prydin/classab-amp/spice/class_ab.asc

C1: cap; 4.7n
C2: cap; 220p
C3: cap; 100n
C4: cap; 220µ
C5: cap; 47p
C6: cap; 1µ
C7: cap; 159.2n
C8: cap; 79.62n
C9: cap; 79.62n
C11: cap; 470p
C12: cap; 470p
C105: cap; 240µ
C107: cap; 100µ
C111: cap; 12µ
C!: cap; 33µ
D1: diode; 1N4148
D2: diode; 1N4148
D3: diode; 1N4148
D4: diode; 1N4148
D5: diode; 1N4148
D6: schottky; 1N5819
D7: diode; RFUH5TF6S
D8: diode; RFUH5TF6S
L1: ind; 10µ
L2: ind; 1m
L3: ind; 1m
L102: ind; 0.43m
L103: ind; 127m
Q1: npn; BC547B
Q2: npn; BC547B
Q3: pnp; BC557B
Q4: pnp; BC557B
Q5: npn; BC547B
Q6: pnp; BD140C
Q7: npn; BD139C
Q8: npn; BD139C
Q9: npn; BD139C
Q10: npn; MJL3281C
Q11: pnp; BD140C
Q12: pnp; MJL1302C
Q13: npn; BC547B
Q14: pnp; BC557B
R1: res; 2.2k
R2: res; 22k
R3: res; 1k
R4: res; 1k
R5: res; 1k
R6: res; 4.7k
R7: res; 1k
R8: res; 0
R9: res; 22k
R10: res; 150
R11: res; 22k
R12: res; 25k
R13: res; 10k
R14: res; 150
R15: res; 128
R16: res; 0.22
R17: res; 0.22
R18: res; 2k
R19: res; 1.5k
R20: res; 10
R21: res; 10
R22: res; 150
R23: res; 2k
R24: res; 2.2k
R25: res; 10k
R26: res; 10k
R27: res; 2.2k
R28: res; 1k
R29: res; 0.001
R30: res; 0.001
R31: res; 7
R114: res; 6
R118: res; 1.5k
R122: res; 137
V1: voltage; 40
V2: voltage; PULSE(-1 1 0.5m 1n 1n 0.5m 1m); AC 0
V3: voltage; 40
V4: voltage; ""; AC 1
V5: voltage; SINE(0 0.5 1k); AC 0
Named nets: 0, IN, B-, B+, OUT, NEG_IN, FB
.tran 0 300m 50m 0.5u
.four 1k 10 -1 v(out)
.option plotwinsize 0
.ac dec 1000 10 100000k
SPEAKER MODEL
SIMPLE SPEAKER MODEL
