prydin/classab-amp/spice/output_stage.asc

C1: cap; 100n
L1: ind; 10µ
Q1: npn; tip35c
Q2: npn; BD139C
R1: res; 10
R2: res; 10
R3: res; 1k
R4: res; 470
R5: res; 8
V1: voltage; 25
V2: voltage; SINE(0 20 1k)
Named nets: 0
.tran 20m
